CREPP-PLOEMEUR/Conception_Electronique/Projets/Station_meteo/PCB/V1_THT/Base/3D_Gallery/Bottom.png

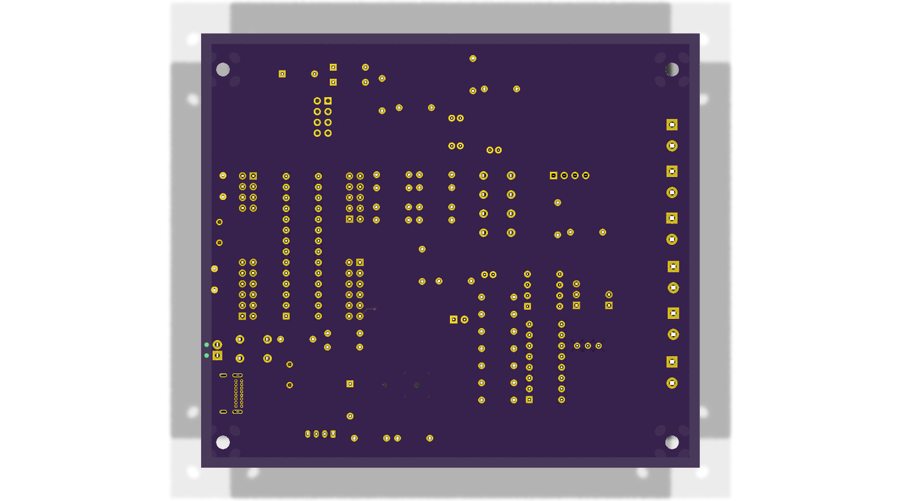
Projets/Station_meteo/PCB/V1_THT/Base/3D_Gallery/Bottom.png
