CREPP-PLOEMEUR/Conception_Electronique/Projets/Station_meteo/PCB/V1_THT/Base/render_side.png

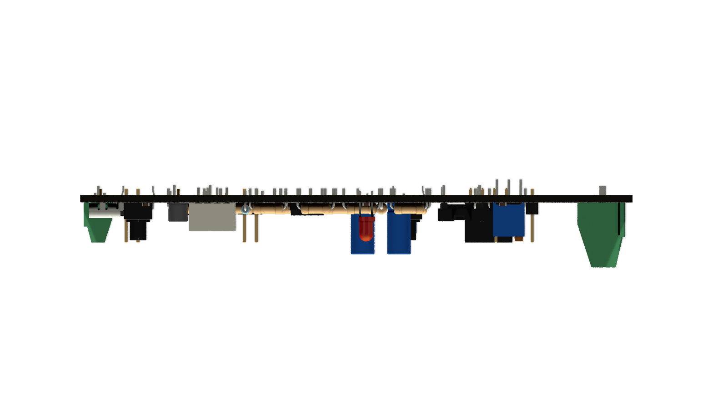
Projets/Station_meteo/PCB/V1_THT/Base/render_side.png
