CREPP-PLOEMEUR/Conception_Electronique/Projets/Station_meteo/SYS_WEATHER.png

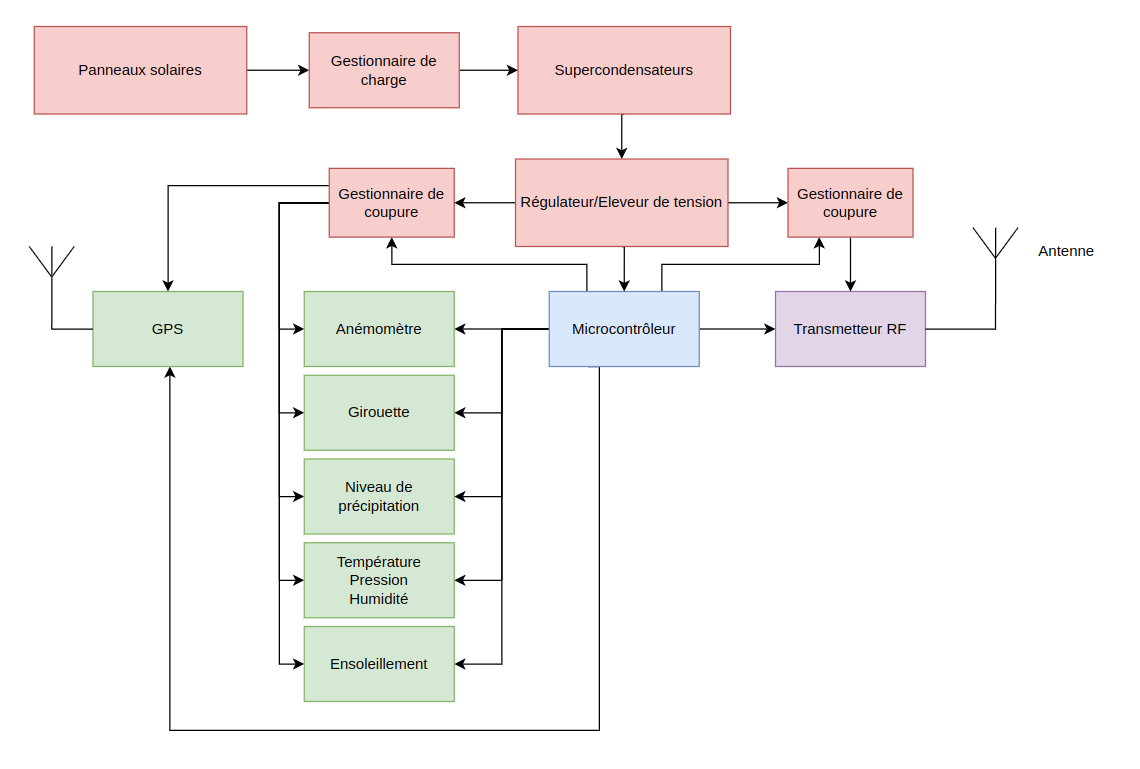
Projets/Station_meteo/SYS_WEATHER.png
