CREPP-PLOEMEUR/Conception_Electronique/Projet_Kicad_steps.png

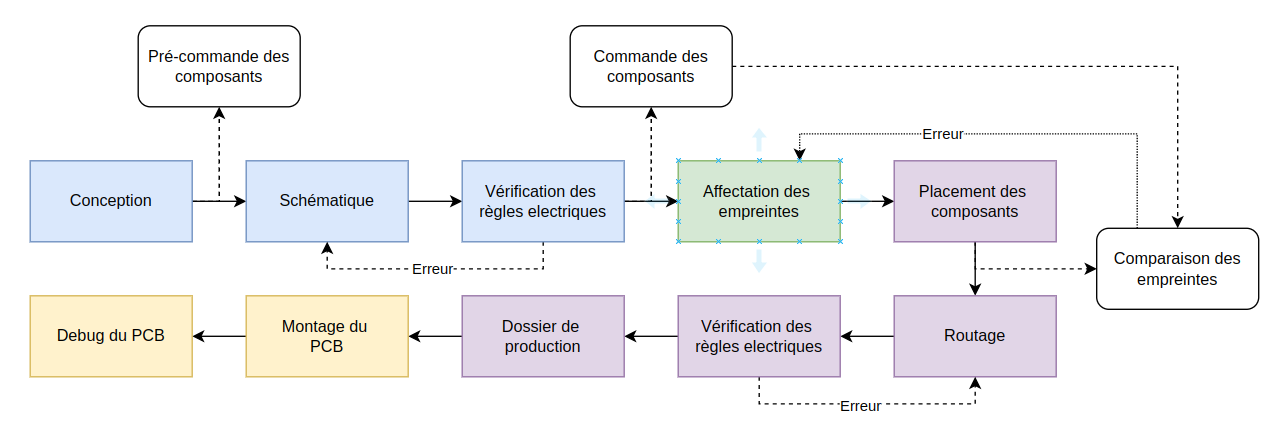
Projet_Kicad_steps.png
